MukeshSankhla/Pathfinder/pathfinder_images/image_33.jpg

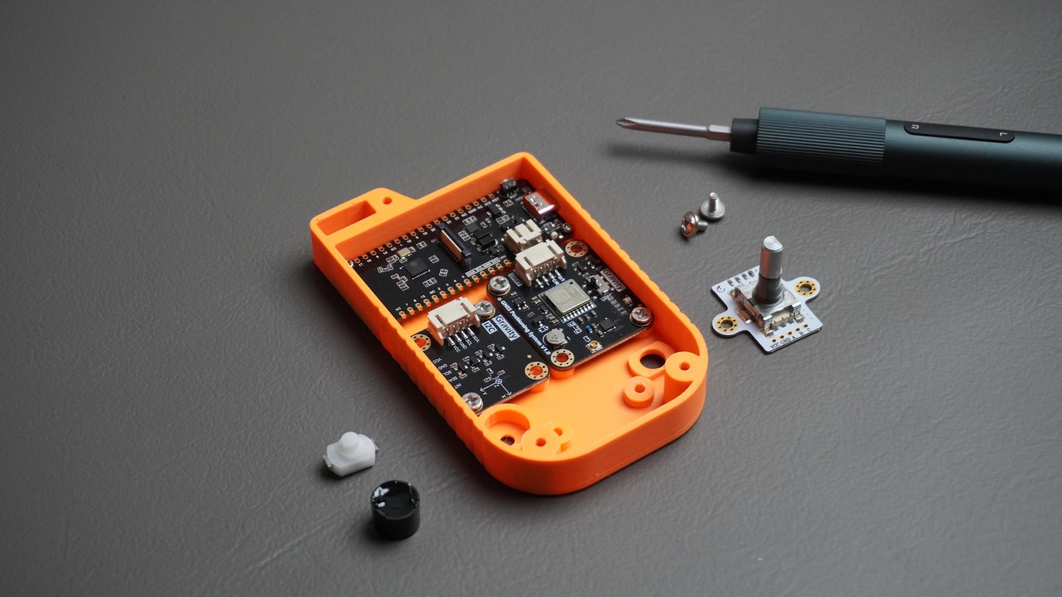
pathfinder_images/image_33.jpg
